n1kdo/BandSelector/src/band_selector/udp_messages.py

__author__ = 'J. B. Otterson'
__copyright__ = """
Copyright 2025, 2026, J. B. Otterson N1KDO.
Redistribution and use in source and binary forms, with or without modification, 
are permitted provided that the following conditions are met:
  1. Redistributions of source code must retain the above copyright notice, 
     this list of conditions and the following disclaimer.
  2. Redistributions in binary form must reproduce the above copyright notice, 
     this list of conditions and the following disclaimer in the documentation 
     and/or other materials provided with the distribution.
THIS SOFTWARE IS PROVIDED BY THE COPYRIGHT HOLDERS AND CONTRIBUTORS "AS IS" AND 
ANY EXPRESS OR IMPLIED WARRANTIES, INCLUDING, BUT NOT LIMITED TO, THE IMPLIED
WARRANTIES OF MERCHANTABILITY AND FITNESS FOR A PARTICULAR PURPOSE ARE DISCLAIMED.
IN NO EVENT SHALL THE COPYRIGHT HOLDER OR CONTRIBUTORS BE LIABLE FOR ANY DIRECT,
INDIRECT, INCIDENTAL, SPECIAL, EXEMPLARY, OR CONSEQUENTIAL DAMAGES (INCLUDING,
BUT NOT LIMITED TO, PROCUREMENT OF SUBSTITUTE GOODS OR SERVICES; LOSS OF USE, 
DATA, OR PROFITS; OR BUSINESS INTERRUPTION) HOWEVER CAUSED AND ON ANY THEORY OF
LIABILITY, WHETHER IN CONTRACT, STRICT LIABILITY, OR TORT (INCLUDING NEGLIGENCE 
OR OTHERWISE) ARISING IN ANY WAY OUT OF THE USE OF THIS SOFTWARE, EVEN IF ADVISED
OF THE POSSIBILITY OF SUCH DAMAGE.
"""
__version__ = '0.0.8'  # 2026-07-16

import asyncio
import micro_logging as logging
import socket
from struct import calcsize, pack_into, unpack
from ringbuf_queue import RingbufQueue


'''
        payload = {'radio_1_antenna': antennas_selected[0],  # is int (0->8), could be uint8
                   'radio_2_antenna': antennas_selected[1],  # is int (0->8), could be uint8
                   'radio_names': config['radio_names'],     # 2x16 char limit from UI
                   'antenna_names': config['antenna_names'], # 8x20 char limit from UI
                   'antenna_bands': config['antenna_bands'], # 8x int, could be uint16
                   'hostname': config['hostname'],           # 64 char limit from UI
                   }
'''
# uint8 uint8 16s 16s 20s 20s 20s 20s 20s 20s 20s 20s hhhhhhhh64s
STATUS_BROADCAST_FMT = 'BB16s16s20s20s20s20s20s20s20s20shhhhhhhh64s'
STATUS_BROADCAST_SIZE = calcsize(STATUS_BROADCAST_FMT)
RADIO_1_ANTENNA_OFFSET = 0
RADIO_2_ANTENNA_OFFSET = 1
RADIO_NAMES_OFFSET = 2
RADIO_NAMES_SIZE = 2
ANTENNA_NAMES_OFFSET = 4
ANTENNA_NAMES_SIZE = 8
ANTENNA_BANDS_OFFSET = 12
ANTENNA_BANDS_SIZE = 8
SWITCH_NAME_OFFSET = 20


def calculate_broadcast_address(ip_address, netmask):
    # validate quick sanity of inputs
    try:
        ip_parts = [int(x) for x in ip_address.split('.')]
        mask_parts = [int(x) for x in netmask.split('.')]
        if len(ip_parts) != 4 or len(mask_parts) != 4:
            raise ValueError('invalid ip or netmask format')
    except Exception as ex:
        logging.error(f'calculate_broadcast_address: invalid input: {ex}', 'udp_messages:calculate_broadcast_address')
        raise

    ip_int = sum([int(x) << 8 * i for i, x in enumerate(reversed(ip_address.split('.')))])
    mask_int = sum([int(x) << 8 * i for i, x in enumerate(reversed(netmask.split('.')))])
    mask_mask = mask_int ^ 0xffffffff
    bcast_int = ip_int | mask_mask
    bcast_addr = ".".join(map(str, [
        ((bcast_int >> 24) & 0xff),
        ((bcast_int >> 16) & 0xff),
        ((bcast_int >> 8) & 0xff),
        (bcast_int & 0xff),
    ]))
    return bcast_addr

def _fit_and_encode(s, length):
    """Encode string to bytes, truncate or pad with NUL to length."""
    if s is None:
        s = bytes(length)
    else:
        if isinstance(s, str):
            s = s.encode('utf-8', 'ignore')
    if len(s) > length:
        s = s[0:length]
    if len(s) < length:
        s = s + (b'\x00' * (length - len(s)))
    return s


class SendBroadcasts:
    """
    class to send UDP status datagrams
    """

    def __init__(self, target_ip, target_port, config: dict, antennas_selected: list):
        self.socket = socket.socket(socket.AF_INET, socket.SOCK_DGRAM)
        self.socket.setsockopt(socket.SOL_SOCKET, socket.SO_BROADCAST, 1)
        self.socket.setsockopt(socket.SOL_SOCKET, socket.SO_REUSEADDR, 1)
        self.sockaddr = socket.getaddrinfo(target_ip, target_port)[0][-1]
        self.config = config
        self.antennas_selected = antennas_selected
        self.buf = bytearray(STATUS_BROADCAST_SIZE)
        logging.info(f'Broadcast address is {target_ip}:{target_port}', 'udp_messages:SendBroadcasts()')
        logging.info(f'Starting status broadcasts', 'udp_messages:SendBroadcasts()')
        self.run = True

    def send(self, payload):
        try:
            self.socket.sendto(payload, self.sockaddr)
        except OSError as ose:
            logging.error(f'UDP Broadcast send failed: OSError {ose}', 'udp_messages:send_datagrams')

    async def send_datagrams(self):
        buf = self.buf
        sleep = asyncio.sleep
        while self.run:
            radio_names = self.config['radio_names']
            antenna_names = self.config['antenna_names']
            antenna_bands = self.config['antenna_bands']
            antennas_selected = self.antennas_selected
            hostname = self.config['hostname']
            #if logging.should_log(logging.DEBUG):
            #    logging.debug(f'radio_names: {radio_names}', 'udp_messages:send_datagrams')
            #    logging.debug(f'antenna_names: {antenna_names}', 'udp_messages:send_datagrams')
            #    logging.debug(f'antenna_bands: {antenna_bands}', 'udp_messages:send_datagrams')
            #    logging.debug(f'antennas_selected: {antennas_selected[0]}, {antennas_selected[1]}',
            #                  'udp_messages:send_datagrams')
            #    logging.debug(f'hostname: {hostname}', 'udp_messages:send_datagrams')
            try:
                pack_into(STATUS_BROADCAST_FMT, buf, 0,
                          int(antennas_selected[0]),
                          int(antennas_selected[1]),
                          _fit_and_encode(radio_names[0] if len(radio_names) > 0 else '', 16),
                          _fit_and_encode(radio_names[1] if len(radio_names) > 1 else '', 16),
                          _fit_and_encode(antenna_names[0] if len(antenna_names) > 0 else '', 20),
                          _fit_and_encode(antenna_names[1] if len(antenna_names) > 1 else '', 20),
                          _fit_and_encode(antenna_names[2] if len(antenna_names) > 2 else '', 20),
                          _fit_and_encode(antenna_names[3] if len(antenna_names) > 3 else '', 20),
                          _fit_and_encode(antenna_names[4] if len(antenna_names) > 4 else '', 20),
                          _fit_and_encode(antenna_names[5] if len(antenna_names) > 5 else '', 20),
                          _fit_and_encode(antenna_names[6] if len(antenna_names) > 6 else '', 20),
                          _fit_and_encode(antenna_names[7] if len(antenna_names) > 7 else '', 20),
                          int(antenna_bands[0]) if len(antenna_bands) > 0 else 0,
                          int(antenna_bands[1]) if len(antenna_bands) > 1 else 0,
                          int(antenna_bands[2]) if len(antenna_bands) > 2 else 0,
                          int(antenna_bands[3]) if len(antenna_bands) > 3 else 0,
                          int(antenna_bands[4]) if len(antenna_bands) > 4 else 0,
                          int(antenna_bands[5]) if len(antenna_bands) > 5 else 0,
                          int(antenna_bands[6]) if len(antenna_bands) > 6 else 0,
                          int(antenna_bands[7]) if len(antenna_bands) > 7 else 0,
                          _fit_and_encode(hostname, 64))
                # send the raw buffer
                self.send(buf)
            except Exception as ex:
                logging.exception(f'UDP Broadcast pack or send failed', 'udp_messages:send_datagrams', ex)
            await sleep(1.0)

    def stop(self):
        self.run = False
        try:
            self.socket.close()
        except Exception:
            pass


class ReceiveBroadcasts:
    """
    class that receives antenna control UDP messages from BandSelectors.
    """

    def __init__(self, receive_ip, receive_port, message_queue: RingbufQueue, message_id: int, switch_name: bytes):
        self.receive_socket = socket.socket(socket.AF_INET, socket.SOCK_DGRAM)
        self.receive_socket.setsockopt(socket.SOL_SOCKET, socket.SO_REUSEADDR, 1)
        self.msgq = message_queue
        self.msgid = message_id
        self.switch_name = switch_name
        self.last_is_foreign = False
        self.buf = bytearray(STATUS_BROADCAST_SIZE)
        self.last_buf = bytearray(STATUS_BROADCAST_SIZE)
        self.run = True
        try:
            sockaddr = socket.getaddrinfo(receive_ip, receive_port)[0][-1]
            self.receive_socket.bind(sockaddr)
            self.receive_socket.settimeout(0.001)
            logging.info(f'Listening on {receive_ip}:{receive_port}', 'udp_messages:ReceiveBroadcasts.init')
            logging.info(f'Listening for status broadcasts', 'udp_messages:ReceiveBroadcasts.init')
        except Exception as exc:
            logging.exception('problem setting up socket', 'udp_messages:ReceiveBroadcasts.init', exc_info=exc)
            self.run = False
            try:
                self.receive_socket.close()
            except Exception:
                pass

    def invalidate(self):
        """
        invalidate the cached last message.
        """
        self.last_buf[:STATUS_BROADCAST_SIZE] = b'\0' * STATUS_BROADCAST_SIZE

    def set_switch_name(self, name: bytes):
        """
        Update the expected switch name (e.g. changed via the API) and force
        re-validation of the next datagram.
        """
        self.switch_name = name
        self.invalidate()

    async def wait_for_datagram(self):
        while self.run:
            try:
                bytes_in = self.receive_socket.readinto(self.buf)
                if bytes_in != STATUS_BROADCAST_SIZE:
                    if logging.should_log(logging.WARNING):
                        logging.warning(f'received {bytes_in} but expected {STATUS_BROADCAST_SIZE} bytes.',
                                        'udp_messages:ReceiveBroadcasts:wait_for_datagram')
                else:
                    # if logging.should_log(logging.DEBUG):
                    #    logging.debug(f'udp_data "{self.buf}"', 'udp_messages:ReceiveBroadcasts:wait_for_datagram')
                    if self.buf != self.last_buf:
                        self.last_buf[:STATUS_BROADCAST_SIZE] = self.buf
                        stuff = unpack(STATUS_BROADCAST_FMT, self.buf)
                        data = []
                        for item in stuff:
                            if isinstance(item, bytes):
                                item = item.partition(b'\0')[0]
                            data.append(item)
                        #if logging.should_log(logging.DEBUG):
                        #    logging.debug(f'message data "{data}"', 'udp_messages:ReceiveBroadcasts:wait_for_datagram')
                        if data[SWITCH_NAME_OFFSET] == self.switch_name:
                            self.last_is_foreign = False
                            msg = (self.msgid, data)
                            await self.msgq.put(msg)
                        elif not self.last_is_foreign:
                            # A switch we do not own is broadcasting on our port.
                            # Report it once, but queue neither the message nor
                            # heartbeats for it: msg_loop would otherwise treat
                            # the foreign switch as our connected switch.
                            logging.warning(f'unexpected switch name {data[SWITCH_NAME_OFFSET]}, want {self.switch_name}',
                                            'udp_messages:ReceiveBroadcasts:wait_for_datagram')
                            self.last_is_foreign = True
                    else:
                        # Only heartbeat for a buffer validated as ours; the
                        # heartbeat carries no name for msg_loop to check.
                        if not self.last_is_foreign:
                            #logging.debug('unchanged UDP message, sending heartbeat only.', 'udp_messages:ReceiveBroadcasts:wait_for_datagram')
                            msg = (self.msgid, [])
                            await self.msgq.put(msg)

            except OSError:
                # this is a timeout exception, no data was received, this is not abnormal.
                pass
            except Exception as exc:
                logging.exception('problem receiving datagram',
                                  'udp_messages:ReceiveBroadcasts:wait_for_datagram', exc_info=exc)
            await asyncio.sleep(0.1)


    def stop(self):
        self.run = False
        try:
            self.receive_socket.close()
        except Exception:
            pass
