n1kdo/BandSelector/src/band_selector/timer_manager.py

__author__ = 'J. B. Otterson'
__copyright__ = """
Copyright 2025, 2026, J. B. Otterson N1KDO.
Redistribution and use in source and binary forms, with or without modification, 
are permitted provided that the following conditions are met:
  1. Redistributions of source code must retain the above copyright notice, 
     this list of conditions and the following disclaimer.
  2. Redistributions in binary form must reproduce the above copyright notice, 
     this list of conditions and the following disclaimer in the documentation 
     and/or other materials provided with the distribution.
THIS SOFTWARE IS PROVIDED BY THE COPYRIGHT HOLDERS AND CONTRIBUTORS "AS IS" AND 
ANY EXPRESS OR IMPLIED WARRANTIES, INCLUDING, BUT NOT LIMITED TO, THE IMPLIED
WARRANTIES OF MERCHANTABILITY AND FITNESS FOR A PARTICULAR PURPOSE ARE DISCLAIMED.
IN NO EVENT SHALL THE COPYRIGHT HOLDER OR CONTRIBUTORS BE LIABLE FOR ANY DIRECT,
INDIRECT, INCIDENTAL, SPECIAL, EXEMPLARY, OR CONSEQUENTIAL DAMAGES (INCLUDING,
BUT NOT LIMITED TO, PROCUREMENT OF SUBSTITUTE GOODS OR SERVICES; LOSS OF USE, 
DATA, OR PROFITS; OR BUSINESS INTERRUPTION) HOWEVER CAUSED AND ON ANY THEORY OF
LIABILITY, WHETHER IN CONTRACT, STRICT LIABILITY, OR TORT (INCLUDING NEGLIGENCE 
OR OTHERWISE) ARISING IN ANY WAY OUT OF THE USE OF THIS SOFTWARE, EVEN IF ADVISED
OF THE POSSIBILITY OF SUCH DAMAGE.
"""
__version__ = '0.0.3'  # 2026-05-25


from asyncio import create_task, sleep_ms
import micropython
import micro_logging as logging

# taken from https://github.com/micropython/micropython-lib/python-stdlib/inspect/inspect.py
_g = lambda: (yield)
def iscoroutinefunction(obj):
    return isinstance(obj, type(_g))

class Timer:
    """
    Timer class contains information about Timer events.
    """
    indexCounter = -1

    def __init__(self, delay:float, callback, arg=None, auto_reset:bool=False)->None:
        Timer.indexCounter += 1
        self.index = Timer.indexCounter
        self.delay = max(1, int(delay * 10))
        self.remaining = self.delay
        self.auto_reset = auto_reset
        self.callback = callback
        self.argument = arg
        self.coroutine = iscoroutinefunction(callback)


class TimerManager:
    """
    TimerManager provides one-shot or periodic timer function callbacks.
    Note that the resolution is "about" 100 milliseconds.
    """

    def __init__(self):
        self._timers = {}
        self._run = True
        create_task(self._check_timers())

    def add_timer(self, delay, callback, arg, auto_reset=False)->int:
        """
        Adds a new timer.
        :param delay: how long to delay the timer.
        :param callback:  function to execute when timer expires
        :param arg: argument to pass to callback
        :param auto_reset: set True to cause timer to repeat
        :return: the timer index, used to cancel or reset the timer.
        """
        timer = Timer(delay, callback, arg, auto_reset)
        self._timers[timer.index] = timer
        #logging.info(f'added timer {timer.index} for {delay} sec...', 'timer_manager:add_timer')
        return timer.index

    def cancel_timer(self, index:int)->None:
        """
        Cancels a timer by index.
        :param index: the timer to cancel.
        :return: None
        """
        timer = self._timers.get(index)
        if timer is not None:
            del self._timers[index]

    def reset_timer(self, index:int)->None:
        """
        Resets a timer by index.
        :param index:  the timer to reset
        :return: None
        """
        #logging.info(f'timer {index} reset...', 'timer_manager:reset_timer')
        timer = self._timers.get(index)
        if timer is not None:
            timer.remaining = timer.delay

    def stop(self) -> None:
        """
        Shut down the timer processor.
        :return: None
        """
        self._run = False

    @micropython.native
    async def _check_timers(self):
        while self._run:
            delete_list = []
            # Iterate a snapshot: a callback may yield (e.g. awaiting a full
            # message queue), during which msg_loop can add or cancel timers.
            # Mutating the dict mid-iteration would raise and kill this task.
            for timer in list(self._timers.values()):
                if timer.index not in self._timers:
                    # Cancelled after the snapshot was taken; skip it.
                    continue
                timer.remaining -= 1
                if timer.remaining == 0:
                    #logging.info(f'timer {timer.index} timed out...', 'timer_manager:_check_timers')
                    try:
                        if timer.coroutine:
                            await timer.callback(timer.argument)
                        else:
                            timer.callback(timer.argument)
                    except Exception as e:
                        logging.exception('timer callback raised', 'timer_manager:_check_timers', e)
                    if timer.auto_reset:
                        timer.remaining = timer.delay
                    else:
                        delete_list.append(timer.index)
            for index in delete_list:
                # pop(): the timer may already have been cancelled (and removed)
                # while its callback was awaiting.
                self._timers.pop(index, None)
            await sleep_ms(100)
